StoutIEEE/macropad-workshop/images/happy-compile.PNG

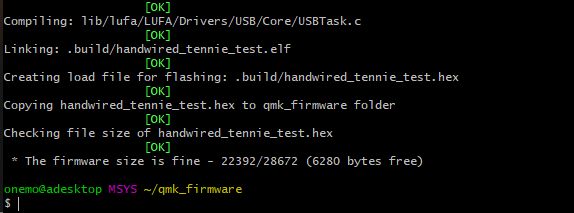
images/happy-compile.PNG
