StoutIEEE/macropad-workshop/images/opened.PNG

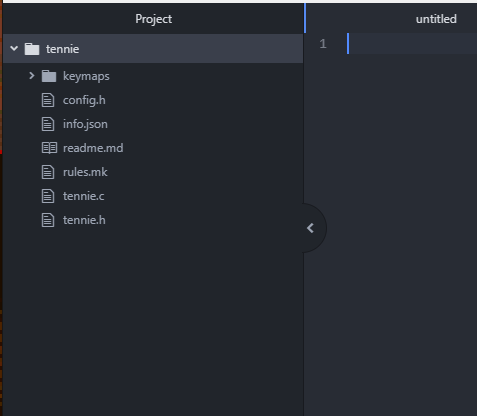
images/opened.PNG
