StoutIEEE/macropad-workshop/images/all-parts.jpg

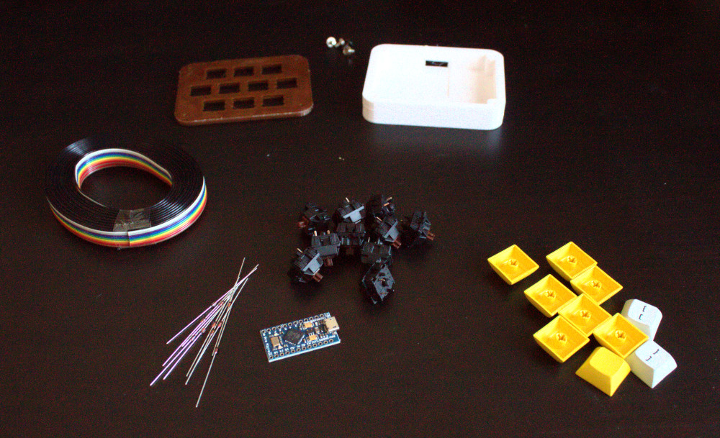
images/all-parts.jpg
