StoutIEEE/macropad-workshop/eagle-files/Macropad.sch

## EAGLE design eagle-files/Macropad.sch (2019-02-22)

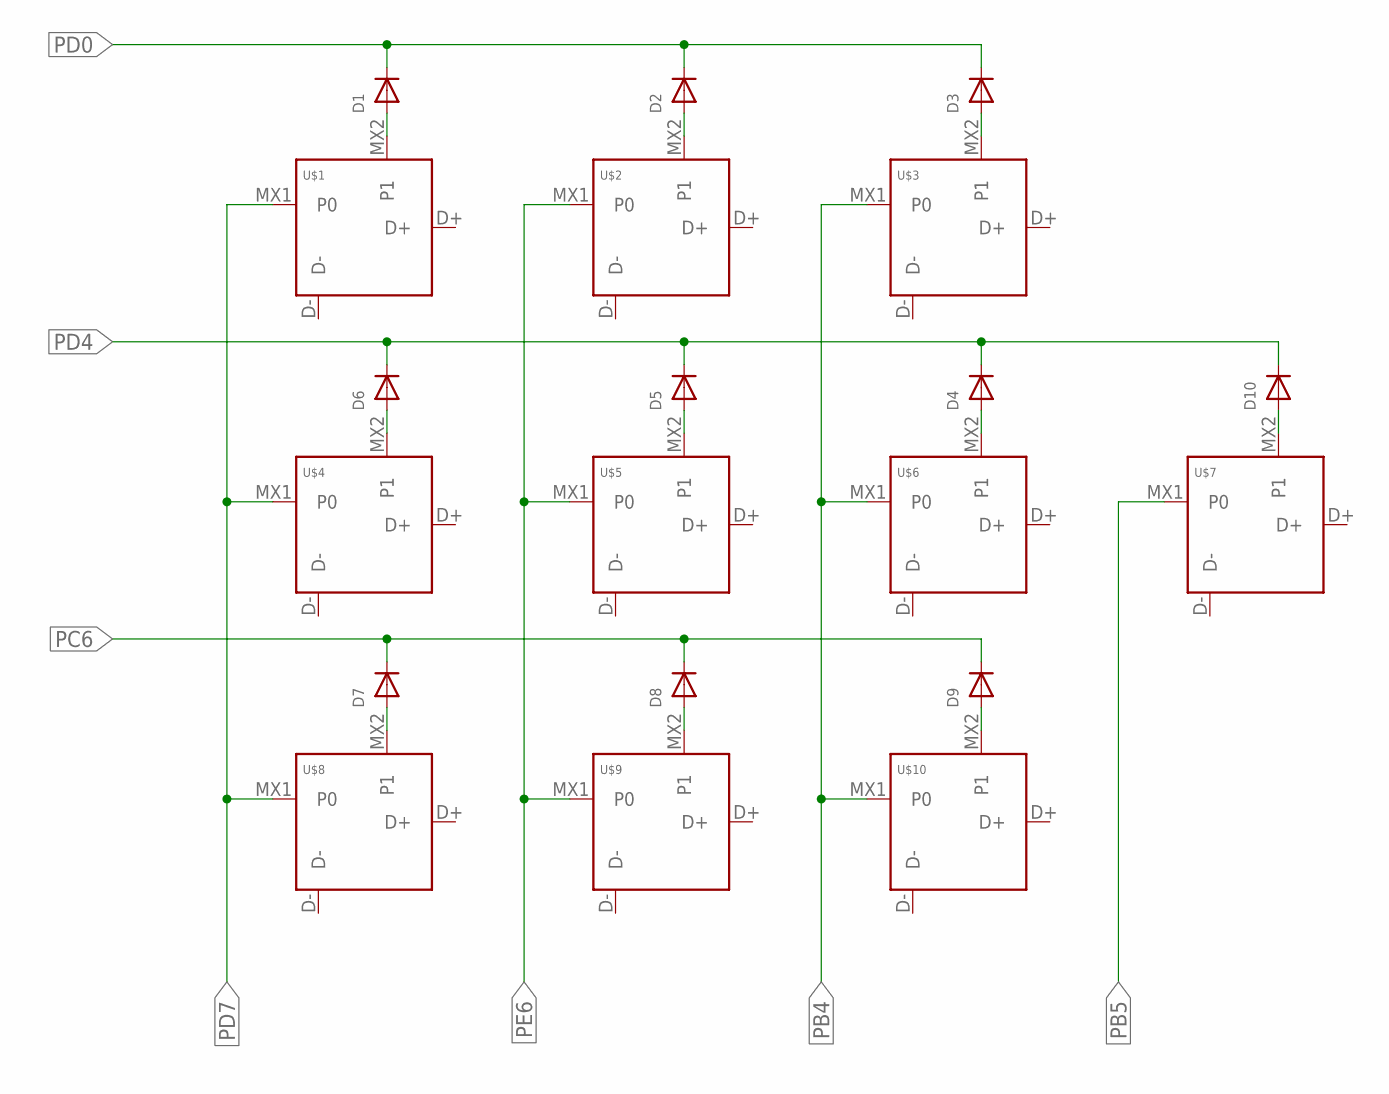
[picture p34: schematic Macropad.sch]

Parts:
D1, D2, D3, D4, D5, D6, D7, D8, D9, D10: DIODEDO-1N4148; DO-1N4148
U$1, U$2, U$3, U$4, U$5, U$6, U$7, U$8, U$9, U$10: KEYSWITCH-DIODE-MX-1U-DIODE; MX-1U-DIODE

Connections:
unnamed: D10.A, U$7.MX2 (P1)
unnamed: D4.A, U$6.MX2 (P1)
unnamed: D9.A, U$10.MX2 (P1)
unnamed: D8.A, U$9.MX2 (P1)
unnamed: D7.A, U$8.MX2 (P1)
unnamed: D6.A, U$4.MX2 (P1)
unnamed: D1.A, U$1.MX2 (P1)
unnamed: D2.A, U$2.MX2 (P1)
unnamed: D3.A, U$3.MX2 (P1)
unnamed: D5.A, U$5.MX2 (P1)
PB4: U$3.MX1 (P0), U$6.MX1 (P0), U$10.MX1 (P0)
PB5: U$7.MX1 (P0)
PC6: D7.C, D8.C, D9.C
PD0: D1.C, D2.C, D3.C
PD4: D4.C, D5.C, D6.C, D10.C
PD7: U$1.MX1 (P0), U$4.MX1 (P0), U$8.MX1 (P0)
PE6: U$2.MX1 (P0), U$5.MX1 (P0), U$9.MX1 (P0)
